ranji0599/M.Tech-Projects/Fusion 360/PNG/Screenshot 2025-03-03 035801.png

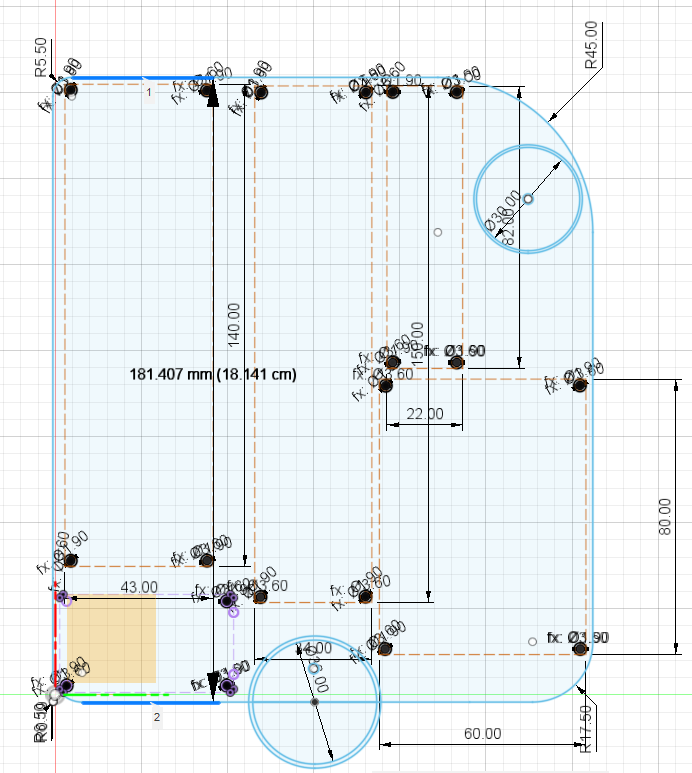
Fusion 360/PNG/Screenshot 2025-03-03 035801.png
